MP120TC/Current_Version/Copal_0_lens_board.stl

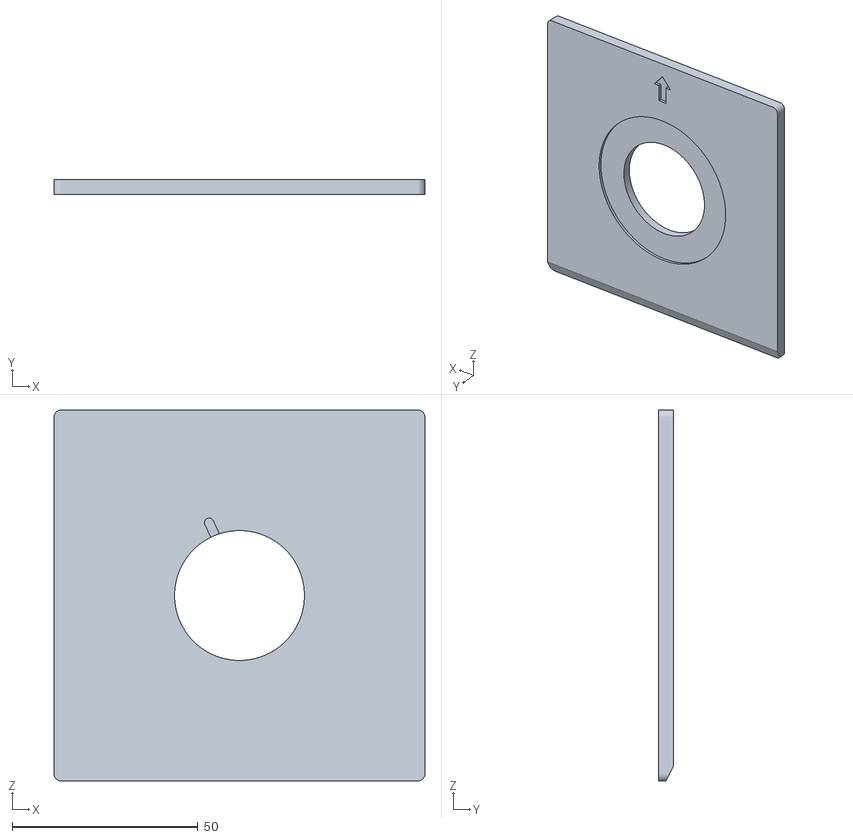
[picture p22: CAD file, 2023-01-13]
Copal_0_lens_board.stl
100.0 x 4.00 x 100.0
