MP120TC/Current_Version/Tilt_knob_cap.stl

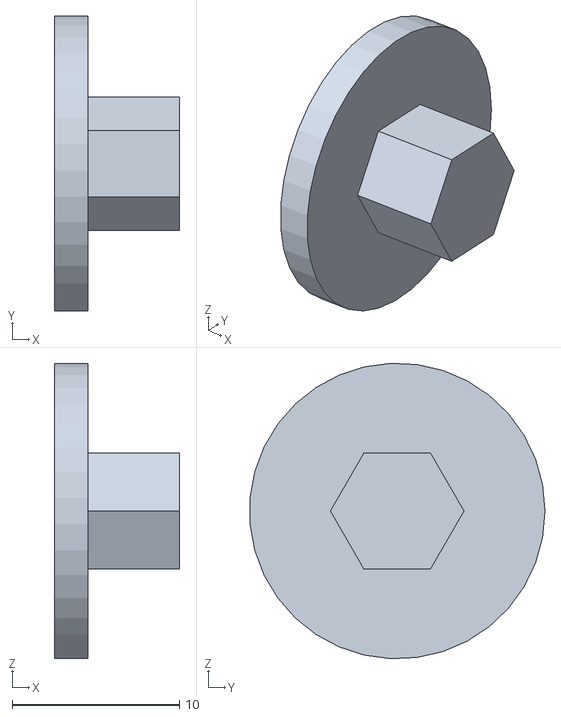
[picture p23: CAD file, 2023-01-13]
Tilt_knob_cap.stl
7.50 x 17.7 x 17.7
