MP120TC/Current_Version/Graflok_Sliding_Plate.stl

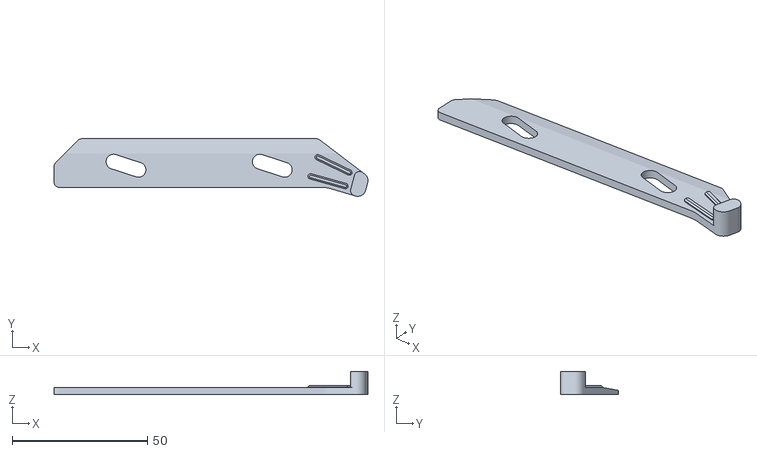
[picture p24: CAD file, 2023-01-13]
Graflok_Sliding_Plate.stl
115.9 x 21.3 x 8.60
