MP120TC/Current_Version/Graflok_Slider-Spacer.stl

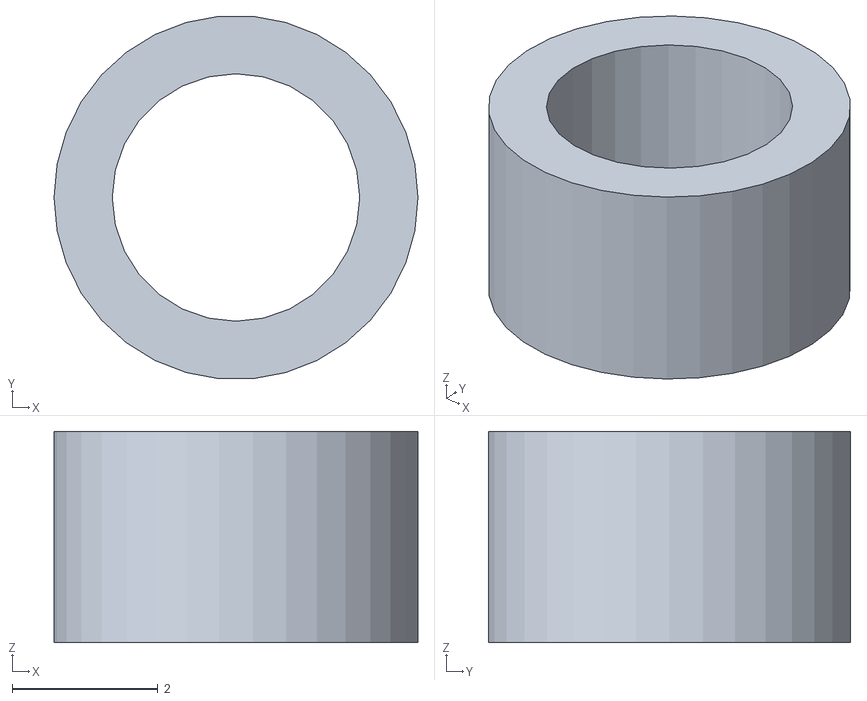
[picture p25: CAD file, 2023-01-13]
Graflok_Slider-Spacer.stl
5.00 x 4.98 x 2.90
