MP120TC/Current_Version/GroundGlassFrame_rear.stl

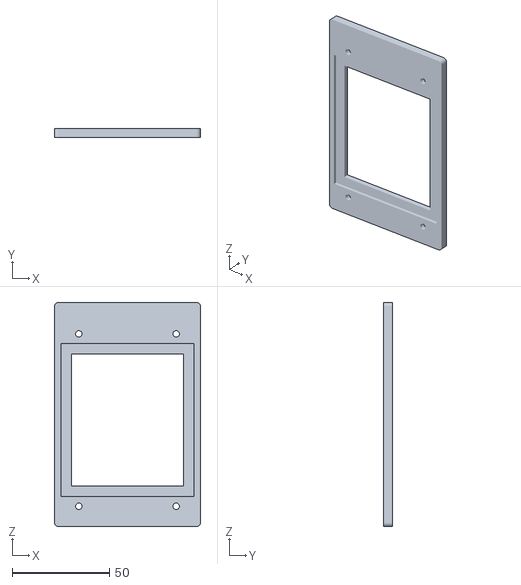
[picture p26: CAD file, 2023-01-13]
GroundGlassFrame_rear.stl
75.0 x 4.50 x 115.0
