MP120TC/Current_Version/Swing_Knob_cap.stl

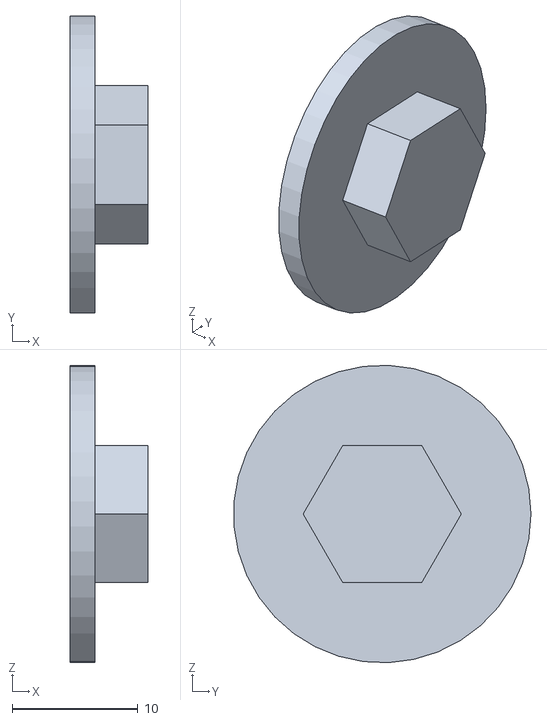
[picture p27: CAD file, 2023-01-13]
Swing_Knob_cap.stl
6.25 x 23.7 x 23.7
