MP120TC/Current_Version/Rear_Rail_Mount.stl

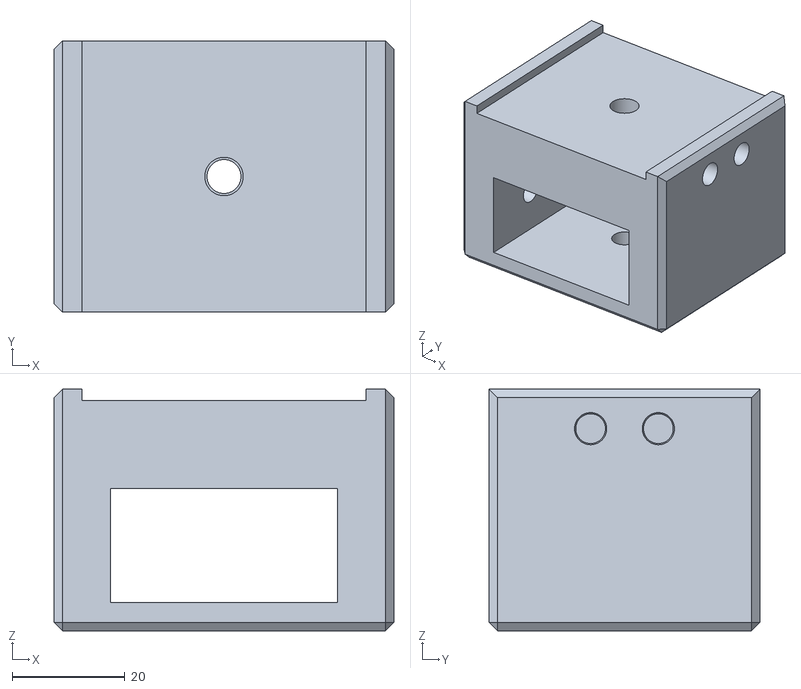
[picture p28: CAD file, 2023-01-13]
Rear_Rail_Mount.stl
60.2 x 48.0 x 42.8
