MP120TC/Current_Version/Swing_Knob.stl

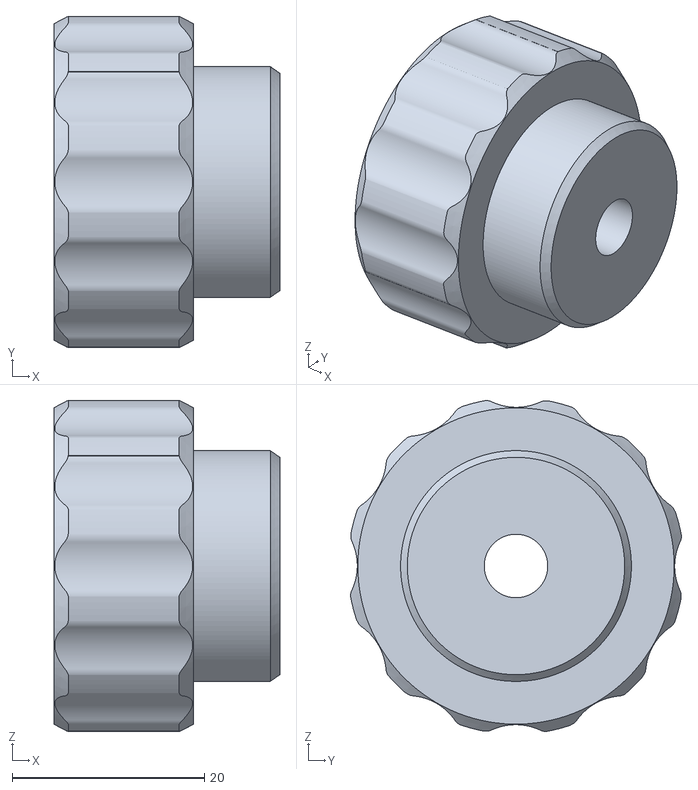
[picture p29: CAD file, 2023-01-13]
Swing_Knob.stl
23.5 x 34.4 x 34.4
