MP120TC/Current_Version/Rail_Tripod_Mount.stl

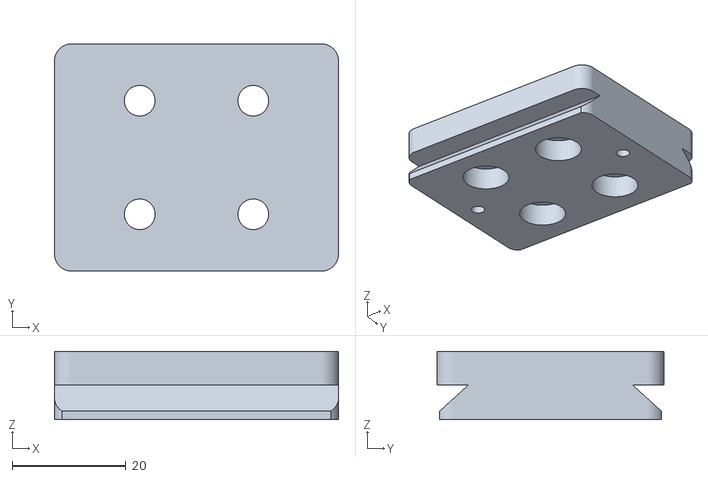
[picture p30: CAD file, 2023-01-13]
Rail_Tripod_Mount.stl
50.0 x 40.0 x 12.0
