MP120TC/Current_Version/GroundGlassFrame_front.stl

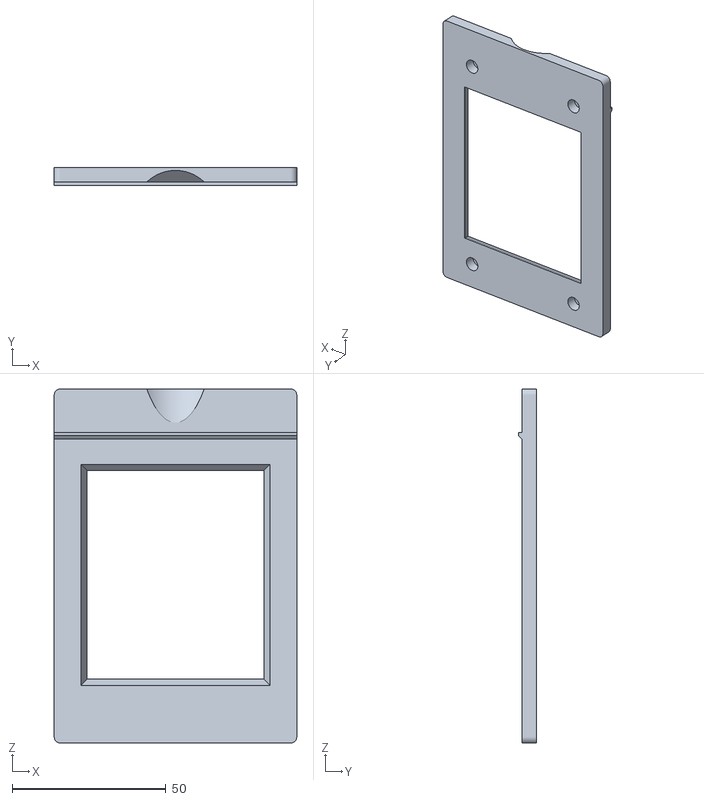
[picture p31: CAD file, 2023-01-13]
GroundGlassFrame_front.stl
78.8 x 5.83 x 115.0
