MP120TC/Current_Version/Rear_Tilt_Block.stl

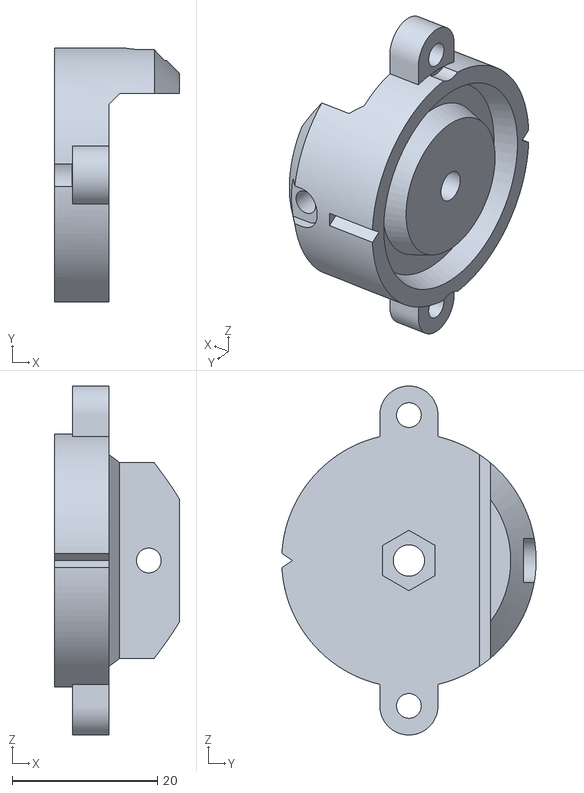
[picture p32: CAD file, 2023-01-13]
Rear_Tilt_Block.stl
17.2 x 35.0 x 48.0
