MP120TC/Current_Version/Frame_QR_Slider.stl

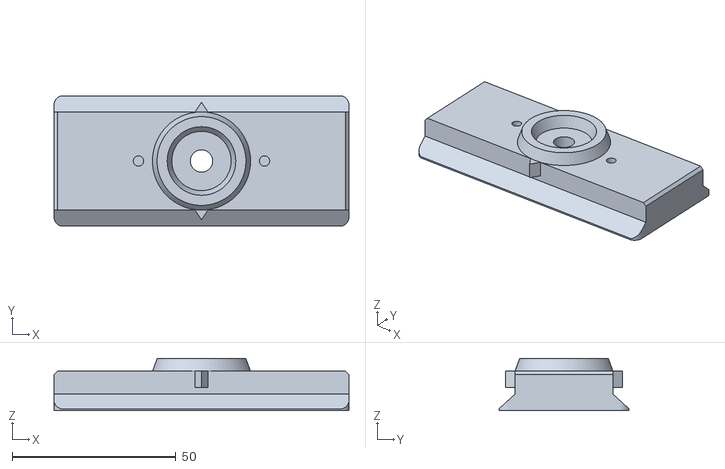
[picture p33: CAD file, 2023-01-13]
Frame_QR_Slider.stl
90.0 x 39.8 x 15.9
