MP120TC/Current_Version/Rise_Fall_Block.stl

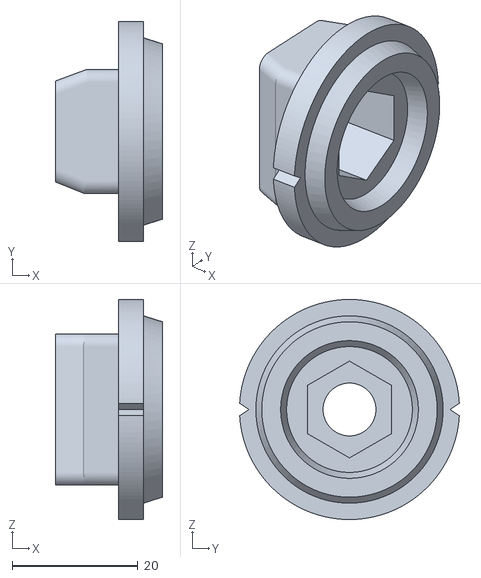
[picture p34: CAD file, 2023-01-13]
Rise_Fall_Block.stl
17.0 x 34.9 x 35.0
