MP120TC/Current_Version/Bellows_Locking_Plate.stl

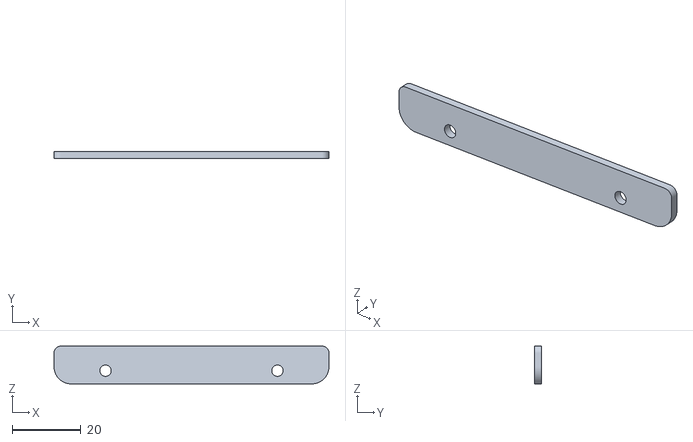
[picture p35: CAD file, 2023-01-13]
Bellows_Locking_Plate.stl
80.0 x 2.00 x 11.0
