MP120TC/Current_Version/Front_Tilt_Block.stl

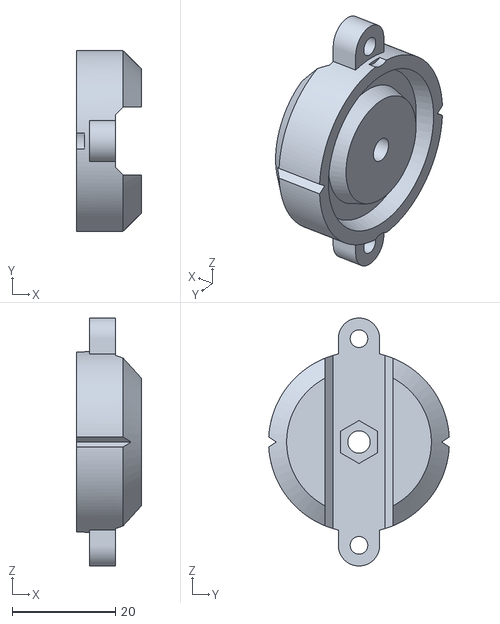
[picture p36: CAD file, 2023-01-13]
Front_Tilt_Block.stl
12.5 x 34.9 x 48.0
