MP120TC/Current_Version/Repositionable_Back.stl

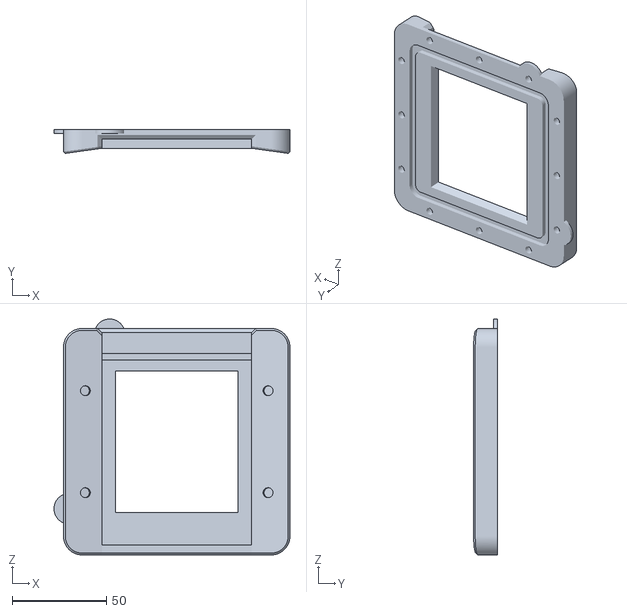
[picture p37: CAD file, 2023-01-13]
Repositionable_Back.stl
125.0 x 12.6 x 125.0
