MP120TC/Current_Version/Bubble_Level_Holder.stl

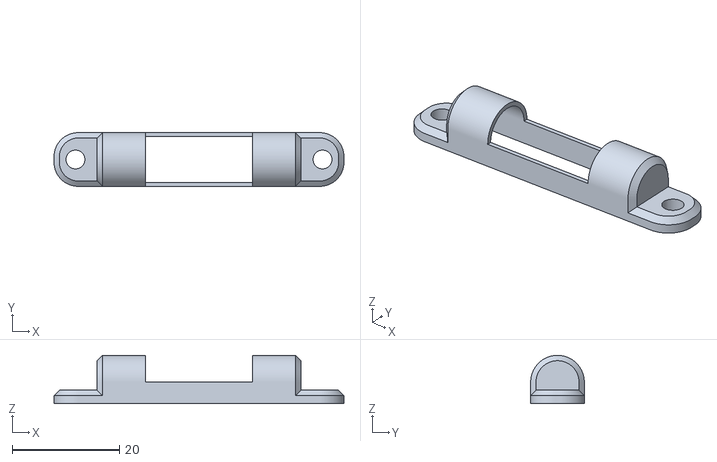
[picture p38: CAD file, 2023-01-13]
Bubble_Level_Holder.stl
54.0 x 10.0 x 9.00
