MP120TC/Current_Version/Rear_L_Arm.stl

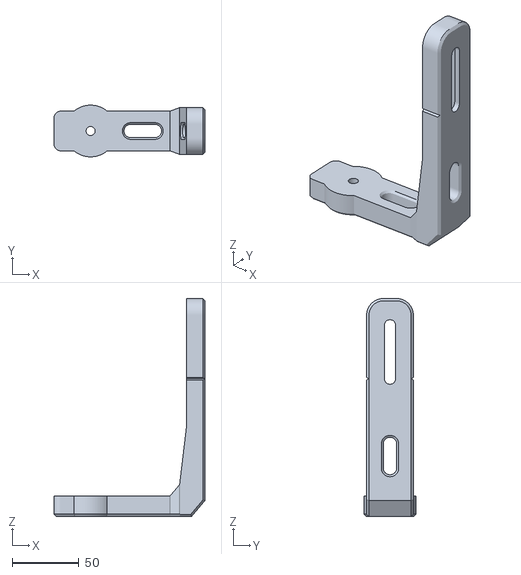
[picture p39: CAD file, 2023-01-13]
Rear_L_Arm.stl
112.9 x 38.7 x 163.0
