MP120TC/Current_Version/Rear_Frame.stl

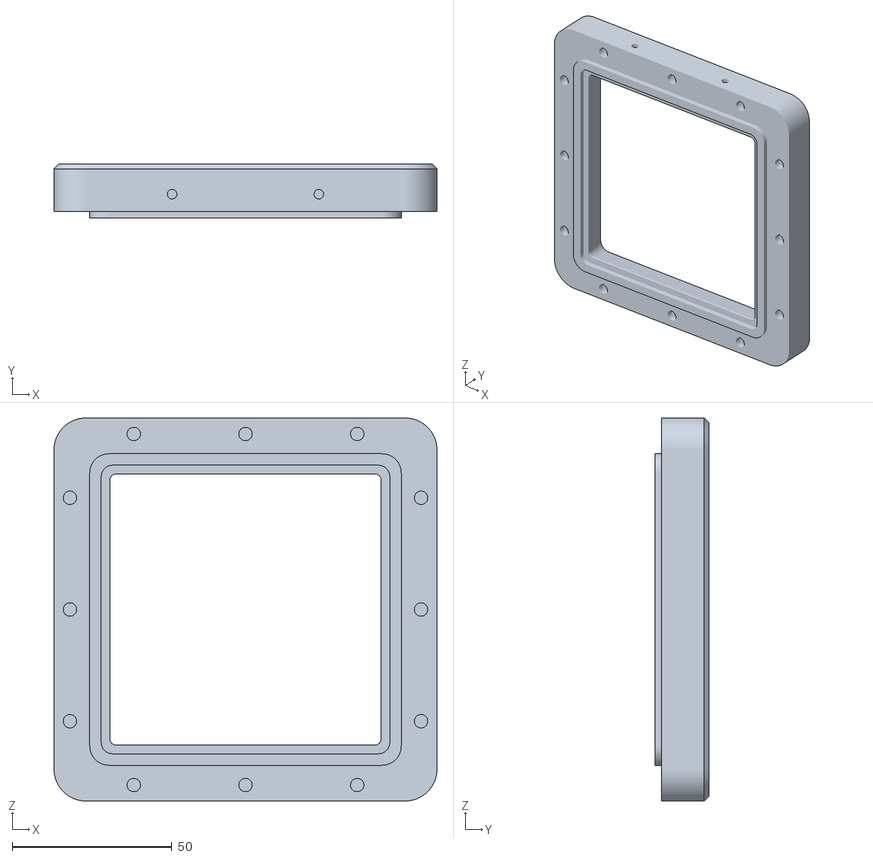
[picture p40: CAD file, 2023-01-13]
Rear_Frame.stl
120.0 x 17.0 x 120.0
