MP120TC/Current_Version/Magnifying_Hood_Tunnel.stl

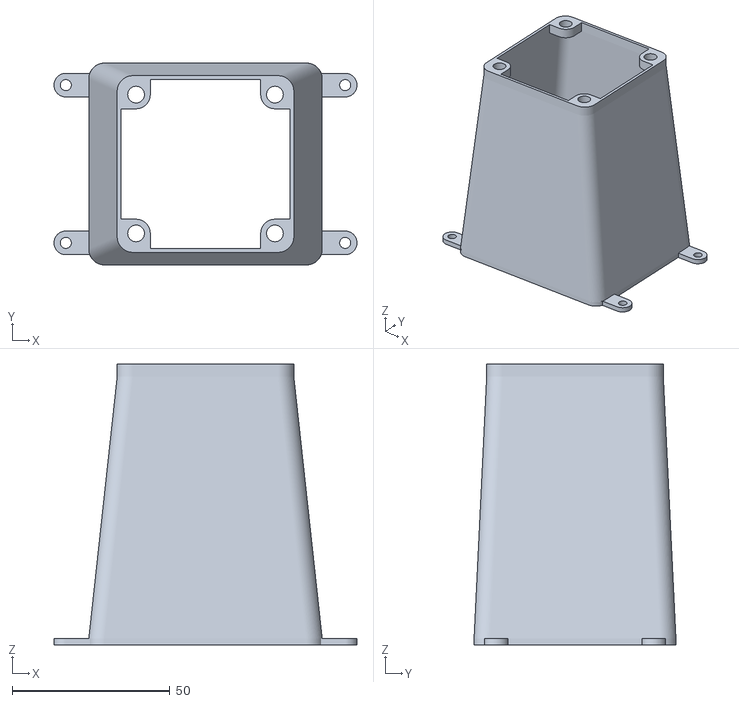
[picture p41: CAD file, 2023-01-13]
Magnifying_Hood_Tunnel.stl
96.0 x 64.0 x 89.0
