MP120TC/Current_Version/Lens_Board_Sliding_Plate.stl

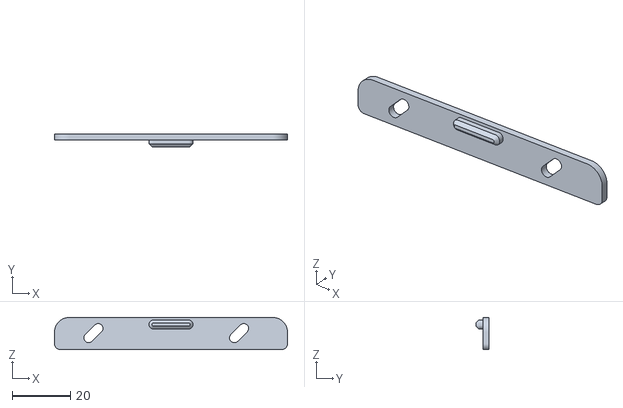
[picture p42: CAD file, 2023-01-13]
Lens_Board_Sliding_Plate.stl
80.0 x 4.50 x 11.0
