MP120TC/Current_Version/Magnifying_Hood_Lower_Lens_Holder.stl

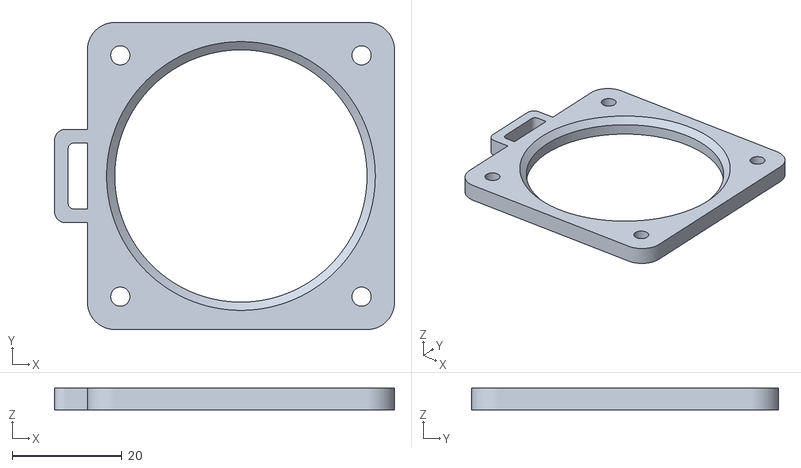
[picture p43: CAD file, 2023-01-13]
Magnifying_Hood_Lower_Lens_Holder.stl
62.0 x 56.0 x 4.00
