MP120TC/Current_Version/Front_L_Arm.stl

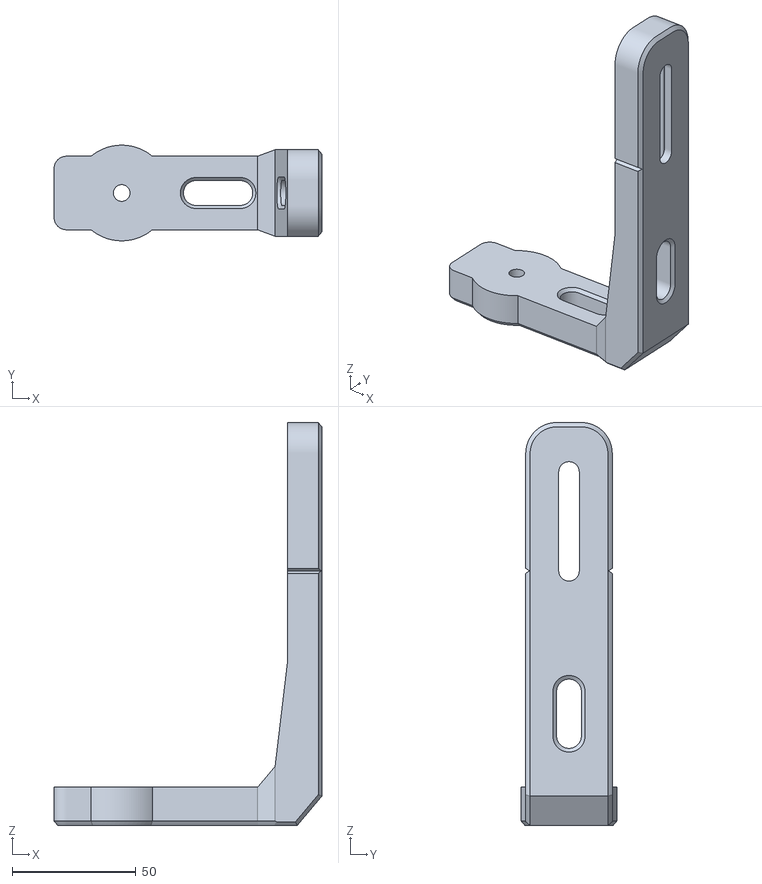
[picture p44: CAD file, 2023-01-13]
Front_L_Arm.stl
108.4 x 38.7 x 163.0
