MP120TC/Current_Version/M8_Plug.stl

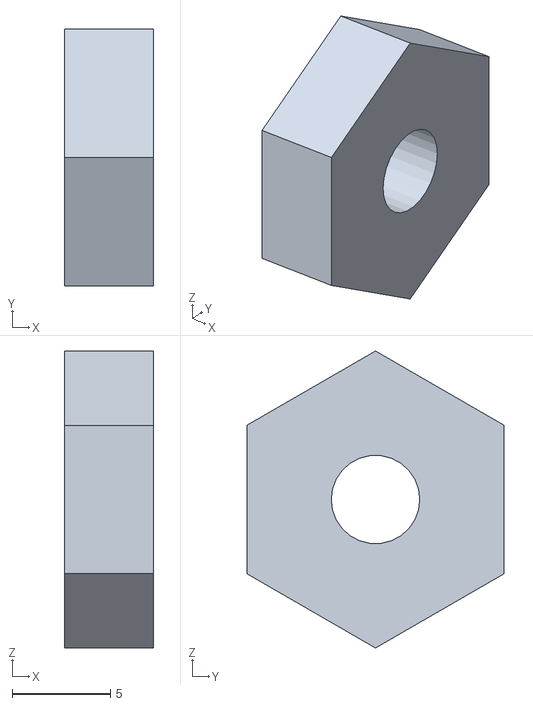
[picture p45: CAD file, 2023-01-13]
M8_Plug.stl
4.50 x 13.1 x 15.1
