MP120TC/Current_Version/Front_Lens_Frame.stl

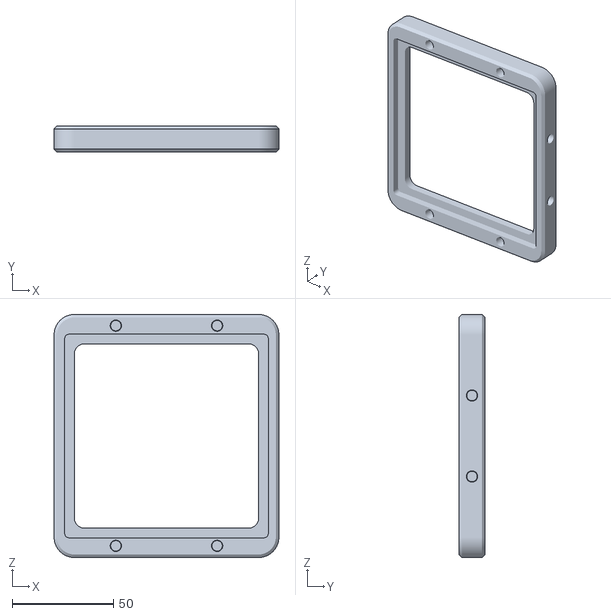
[picture p46: CAD file, 2023-01-13]
Front_Lens_Frame.stl
111.0 x 13.0 x 120.0
