MP120TC/Current_Version/Magnifying_Hood_EyeCup.stl

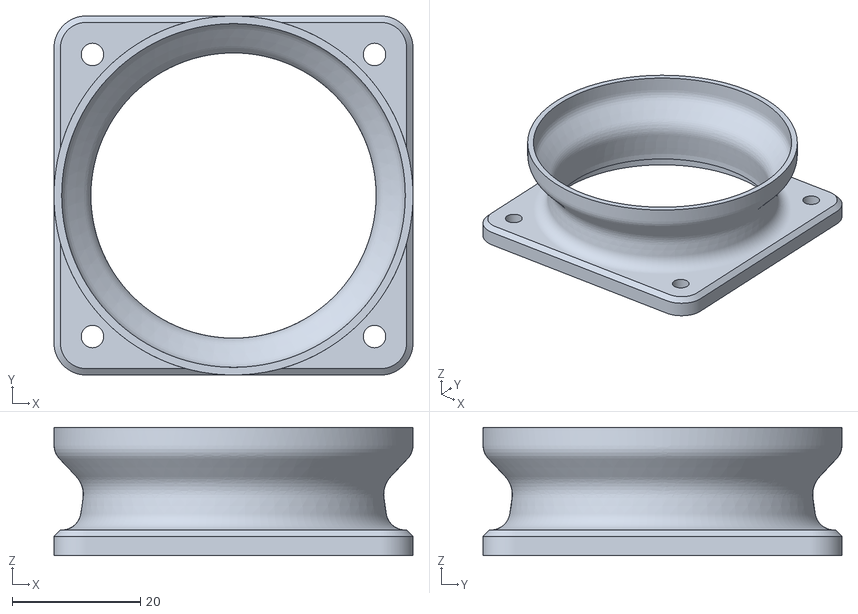
[picture p47: CAD file, 2023-01-13]
Magnifying_Hood_EyeCup.stl
56.0 x 56.0 x 20.0
