MP120TC/Current_Version/Tilt_knob.stl

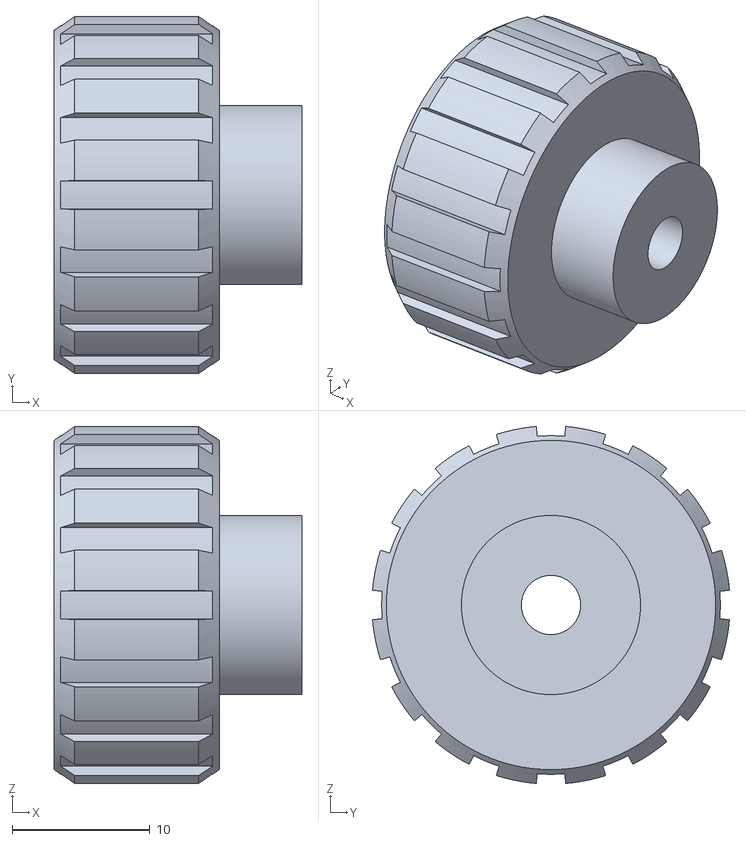
[picture p48: CAD file, 2023-01-13]
Tilt_knob.stl
18.0 x 25.9 x 25.9
