MP120TC/Current_Version/Rise_Fall_knob.stl

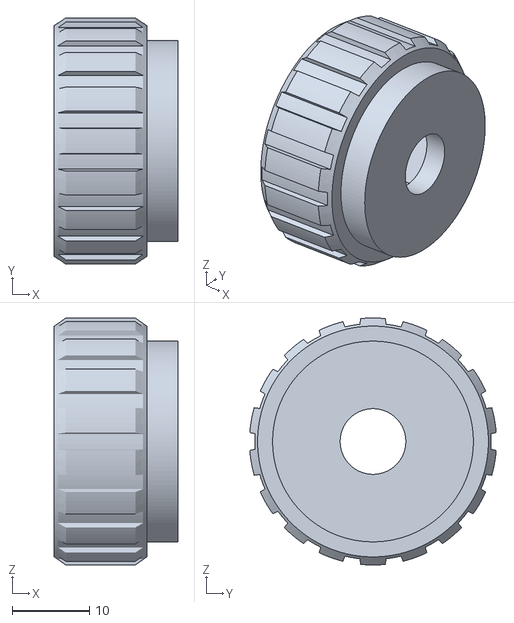
[picture p49: CAD file, 2023-01-13]
Rise_Fall_knob.stl
16.0 x 31.9 x 32.0
